brentb2529/B-Infohub/hardware/pcb/tools/gen_bom.py

"""Write bom_jlc.csv / cpl_jlc.csv from circuit.py.

Rev 1.1: U1 is a soldered ESP32-WROOM-32E, an ordinary SMT line (JLC extended
part). The rev 1.0 socket-row special case is gone.
"""
import csv
from circuit import *
# JLCPCB's part library is rotated relative to KiCad's footprints for these packages. Verified in the JLC
# placement preview on 2026-08-25 (pin-1 mark vs. our copper): SOT-23 needs +180, TSOT-23-6 needs -90 (=270),
# 1xN pin headers need 90, CP_Elec SMD electrolytic needs 180 (JLC "+" opposite to KiCad pad 1). Everything else (0603/0805/1206, SMA, SOD-123, LED 0603, JST-XH, 5.08 terminals,
# SRN6045 inductor, 1812 fuse) matched as-is.
# Rev 1.1 packages, verified in the JLC viewer on 2026-10-01: ESPW (WROOM) needs -90 (=270): JLC's
# library zero has the antenna at -x and our board rotation 270 put it at -y, over the capacitor row;
# 180 total puts it at +x, the board edge. SMA (SS14 band toward F3/+12 V) and SW4 (TS-1187A) matched as-is.
# This project's pin headers are PH2 (JP1/JP2) and PH6 (J4/J6); b-hydro's were PH3/PH4.
# The "1xN pin headers need 90" finding was made on b-hydro's headers, and the
# package family is the same, so the rule is applied to ours -- but it has NOT
# been seen in the JLC viewer for these two footprints. Check J4/J6/JP1/JP2 in
# the placement preview, or hand-solder the THT (ORDER.md offers both).
ROT_FIX={"SOT":180,"TSOT6":270,"PH2":90,"PH6":90,"CPSMD":180,"ESPW":270,"SW4":0,"SMA":0}   # PHX/XH2/XH4 (KF128 terminals): verified 0 in the JLC viewer
rows={}
descs={}
vals={}
for ref,p in sorted(P.items(), key=lambda kv:(kv[0][0],int(''.join(c for c in kv[0][1:] if c.isdigit()) or 0))):
    if ref.startswith("H"): continue
    # Group by FOOTPRINT + LCSC only. Neither the description nor the VALUE may be
    # part of the key: five identical 100 nF caps with five different per-net
    # comments, or two identical terminal blocks whose values are their silk
    # labels (J2 "BUS A B" / J5 "FAN 12V"), would otherwise become separate BOM
    # lines for one part, and JLC flags that as "multiple lines matched to the
    # same part" and deselects the duplicates. Caught in the JLC BOM review on
    # 2026-08-31 (descriptions) and in the rev 1.1 EE review (values).
    key=(FP[p["fp"]][1],"" if p["dnp"] else p["lcsc"])
    rows.setdefault(key,[]).append(ref)
    descs.setdefault(key,[]).append(p["desc"])
    vals.setdefault(key,[]).append(p["value"])
with open("../bom_jlc.csv","w",newline="") as f:
    w=csv.writer(f); w.writerow(["Comment","Designator","Footprint","LCSC Part #","Qty","Assembly","Note","Description"])
    for key,refs in rows.items():
        fp,lcsc = key
        # one Comment per line: the first value, plus the others if they differ
        uv=list(dict.fromkeys(vals[key])); val=uv[0] if len(uv)==1 else uv[0]+" ("+", ".join(uv[1:])+")"
        # keep the longest description: it is the one carrying the reasoning
        desc = max(descs[key], key=len)
        asm="DNP" if not lcsc else ("JLC THT (economic, hand-solder fee)" if any(P[r]["hand"] for r in refs) else "JLC SMT")
        w.writerow([val,",".join(refs),fp,lcsc,len(refs),asm,"",desc])
with open("../cpl_jlc.csv","w",newline="") as f:
    w=csv.writer(f); w.writerow(["Designator","Mid X","Mid Y","Layer","Rotation"])
    for ref,p in sorted(P.items()):
        if ref.startswith("H") or p["dnp"]: continue
        x,y,r=p["pcb"]
        r=(r+ROT_FIX.get(p["fp"],0))%360
        w.writerow([ref,f"{x:.3f}mm",f"{-y:.3f}mm","Top",f"{r:.6f}"])
print("bom rows",len(rows))
